yijieluo/funny_car/funny_car project/bsp/stm32f4xx-HAL/applications/pid.h

/**
  ******************************************************************************
  * @file		 pid.h
  * @author  Ginger
  * @version V1.0.0
  * @date    2015/11/14
  * @brief   
  ******************************************************************************
  * @attention
  *
  ******************************************************************************
  */

/* Includes ------------------------------------------------------------------*/

#ifndef _PID_H
#define _PID_H

#include "stdint.h"
typedef enum
{
	PID_Position,
	PID_Speed
}PID_ID;

typedef struct _PID_TypeDef
{
	PID_ID id;
	
	float target;							//目标值
	float lastNoneZeroTarget;
	float kp;
	float ki;
	float kd;
	
	float   measure;					//测量值
	float   err;							//误差
	float   last_err;      		//上次误差
	
	float pout;
	float iout;
	float dout;
	
	float output;						//本次输出
	float last_output;			//上次输出
	
	float MaxOutput;				//输出限幅
	float IntegralLimit;		//积分限幅
	float DeadBand;			  //死区（绝对值）
	float ControlPeriod;		//控制周期
	float  Max_Err;					//最大误差
	
					uint32_t thistime;
					uint32_t lasttime;
					uint8_t dtime;	
	
	void (*f_param_init)(struct _PID_TypeDef *pid,  //PID参数初始化
				   PID_ID id,
				   float maxOutput,
				   float integralLimit,
				   float deadband,
				   float controlPeriod,
					 float max_err,     
					 float  target,
				   float kp,
				   float ki,
				   float kd);
				   
	void (*f_pid_reset)(struct _PID_TypeDef *pid, float kp,float ki, float kd);		//pid三个参数修改
	float (*f_cal_pid)(struct _PID_TypeDef *pid, float measure, float target);   //pid计算
}PID_TypeDef;

void pid_reset(PID_TypeDef * pid, float kp, float ki, float kd);

void pid_init(void);
#endif
